RBSC/Konami-SCC-Cartridge-Repair/Pics/board.png

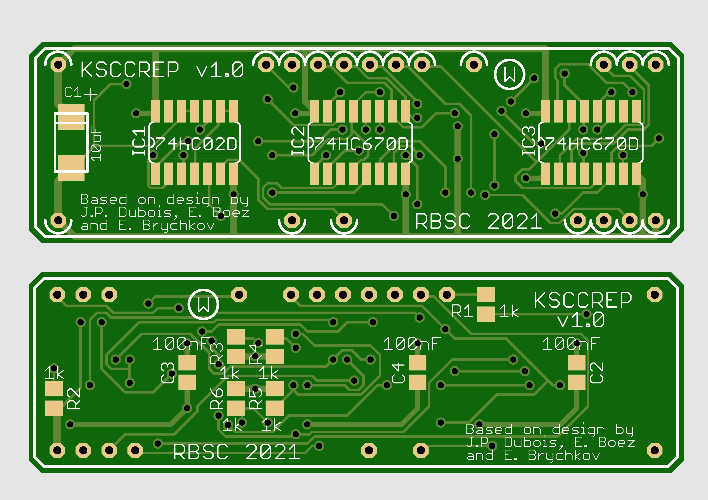
Pics/board.png
