RBSC/Konami-SCC-Cartridge-Repair/Pics/ready_back.jpg

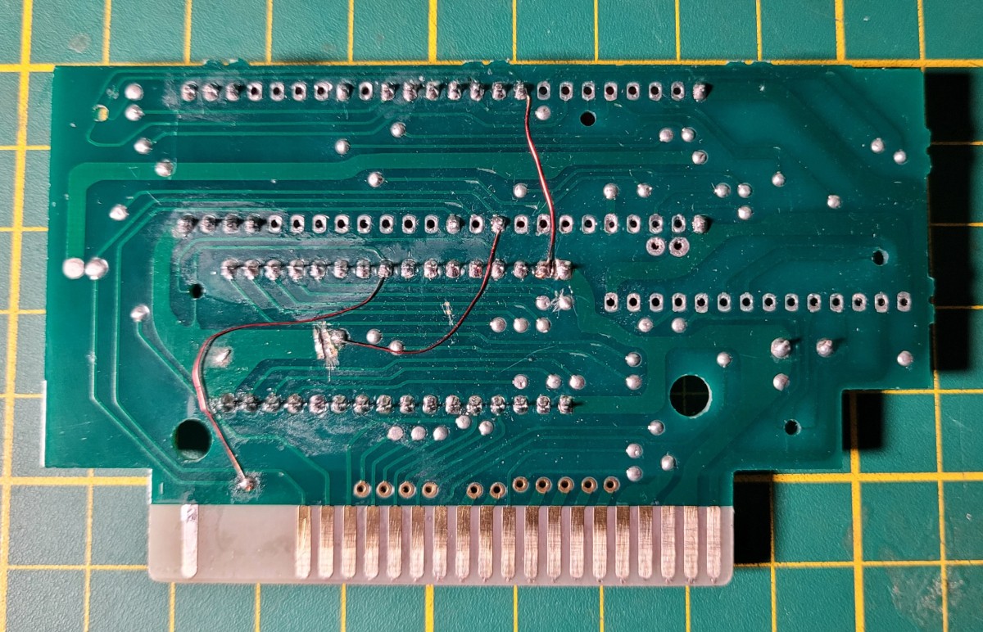
Pics/ready_back.jpg
